TheoBounac/TP-1-Arret-Urgence/images/boitier_emetteur.png

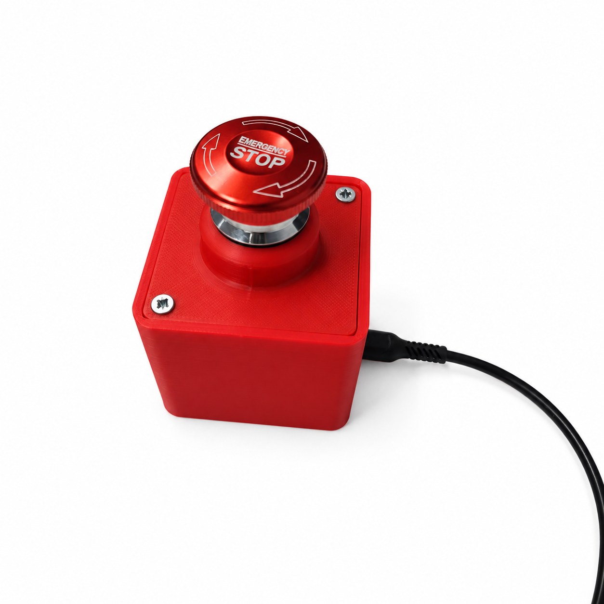
images/boitier_emetteur.png
