TheoBounac/TP-1-Arret-Urgence/images/boitier_recepteur.png

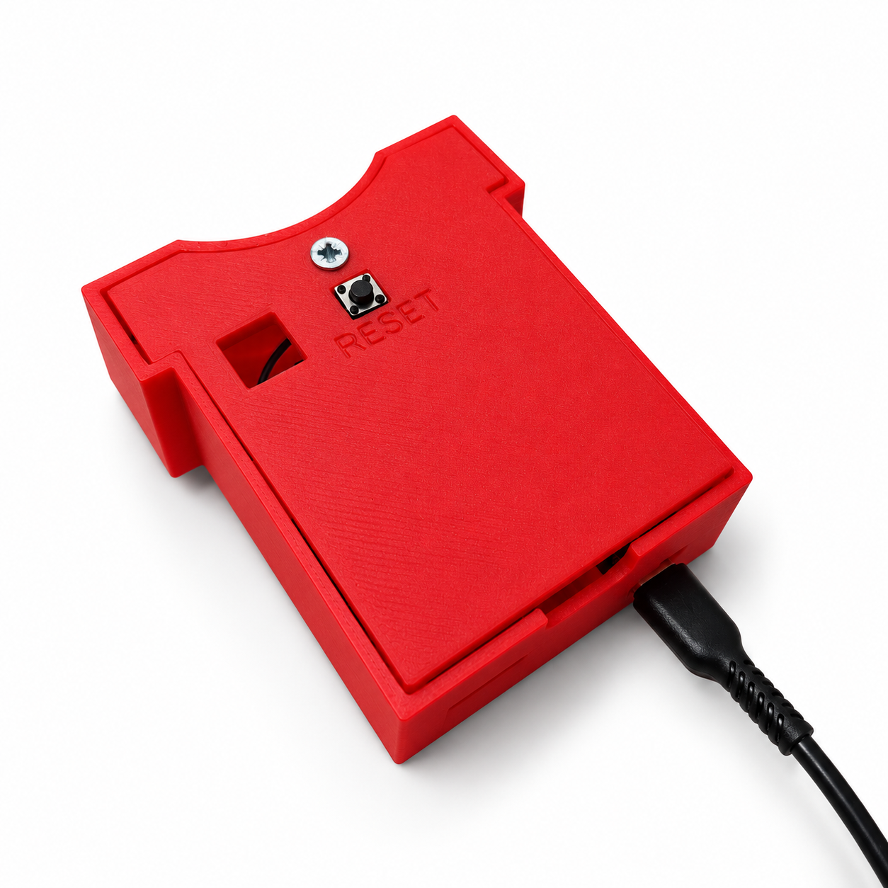
images/boitier_recepteur.png
