TheoBounac/TP-1-Arret-Urgence/images/carte_arduino.png

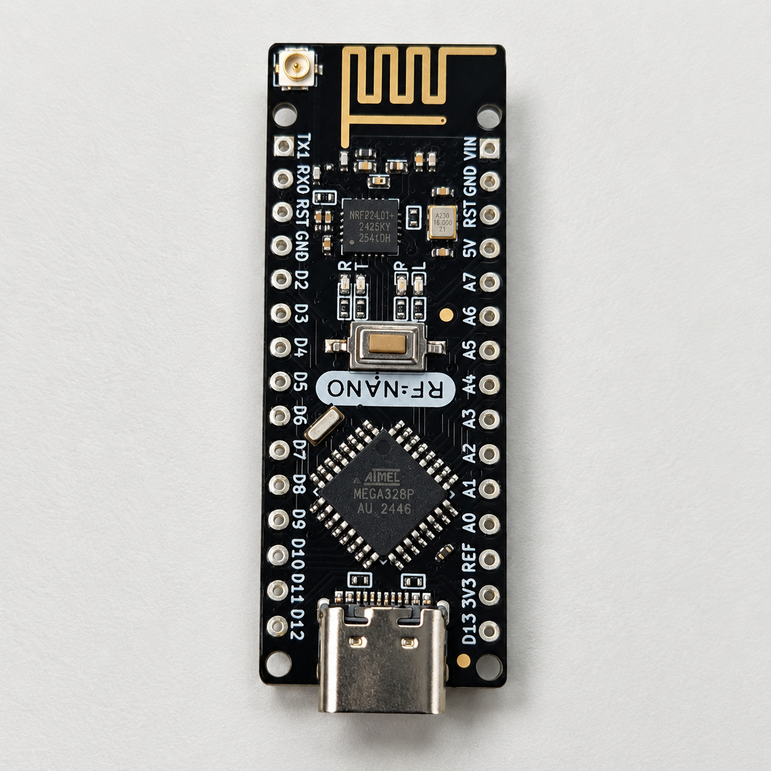
images/carte_arduino.png
