TheoBounac/TP-1-Arret-Urgence/images/cas.png

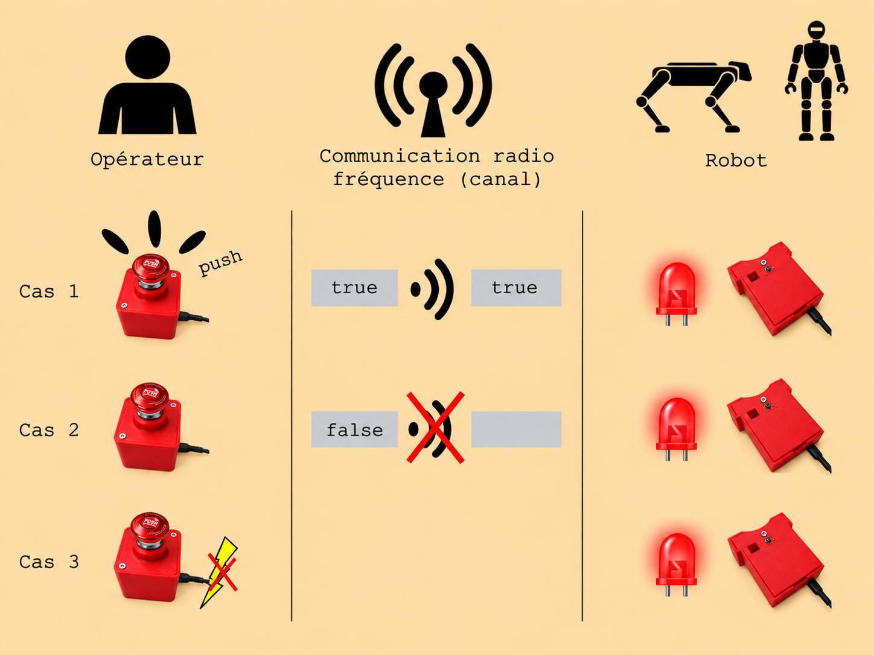
images/cas.png
