TheoBounac/TP-1-Arret-Urgence/images/cas_2.png

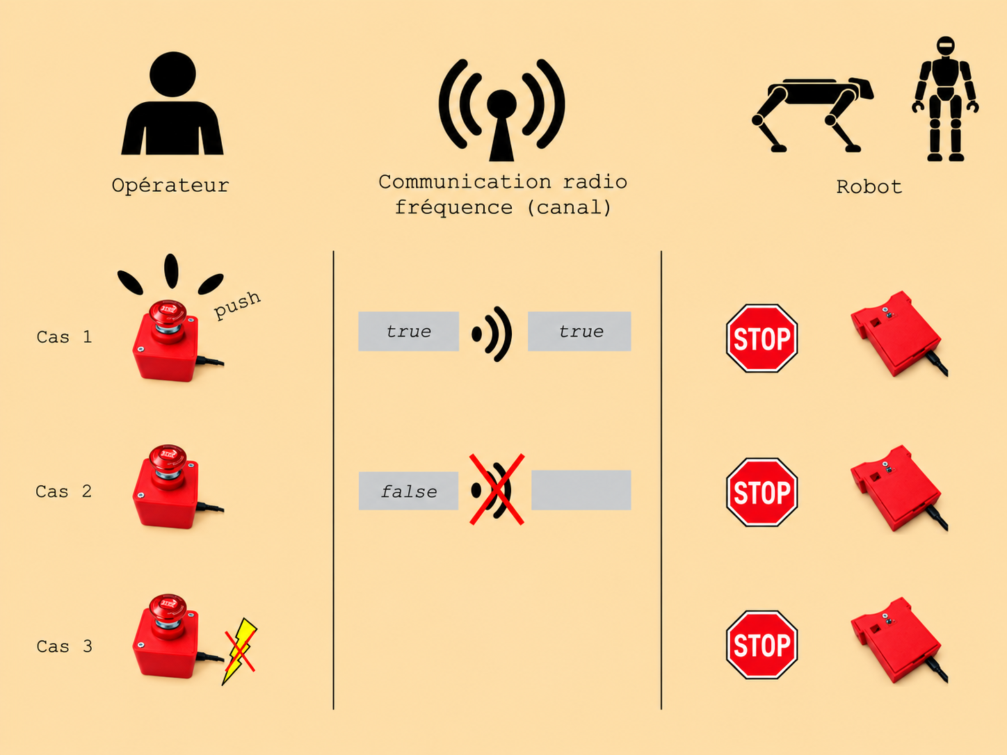
images/cas_2.png
