TheoBounac/TP-1-Arret-Urgence/images/go2.png

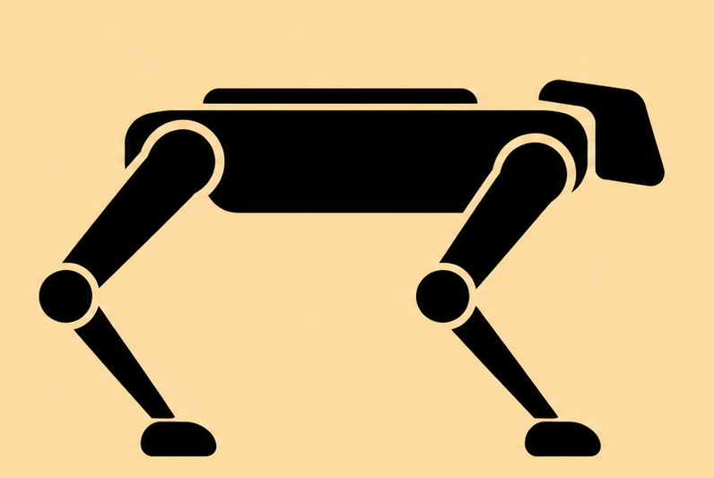
images/go2.png
