TheoBounac/TP-1-Arret-Urgence/images/images.jpeg

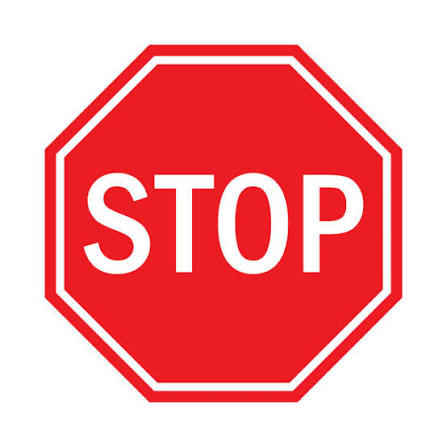
images/images.jpeg
