TheoBounac/TP-1-Arret-Urgence/images/just-got-my-unitree-quadruped-robot-go2-walking-in-isaac-v0-8nw8yerlim7g1.png

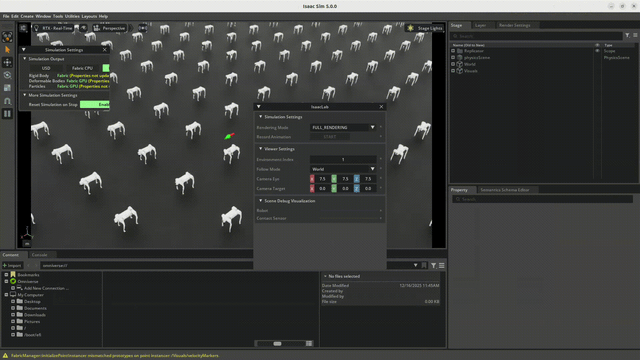
images/just-got-my-unitree-quadruped-robot-go2-walking-in-isaac-v0-8nw8yerlim7g1.png
