TheoBounac/TP-1-Arret-Urgence/images/orig.webp

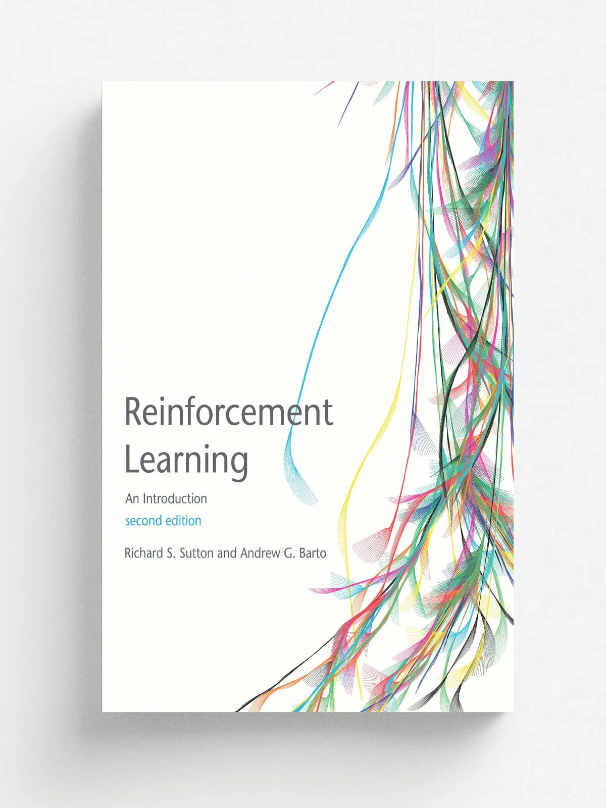
images/orig.webp
