TheoBounac/TP-1-Arret-Urgence/images/receptteur_cable.png

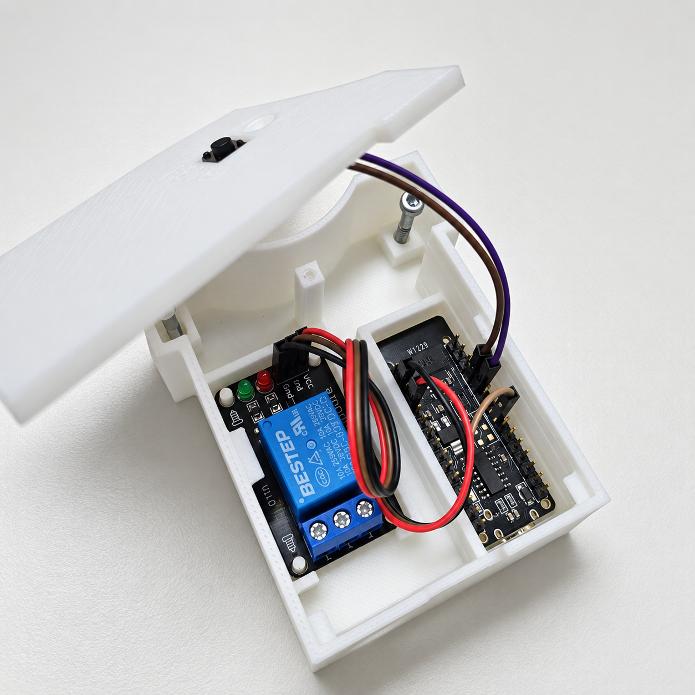
images/receptteur_cable.png
