TheoBounac/TP-1-Arret-Urgence/images/relais_ex.png

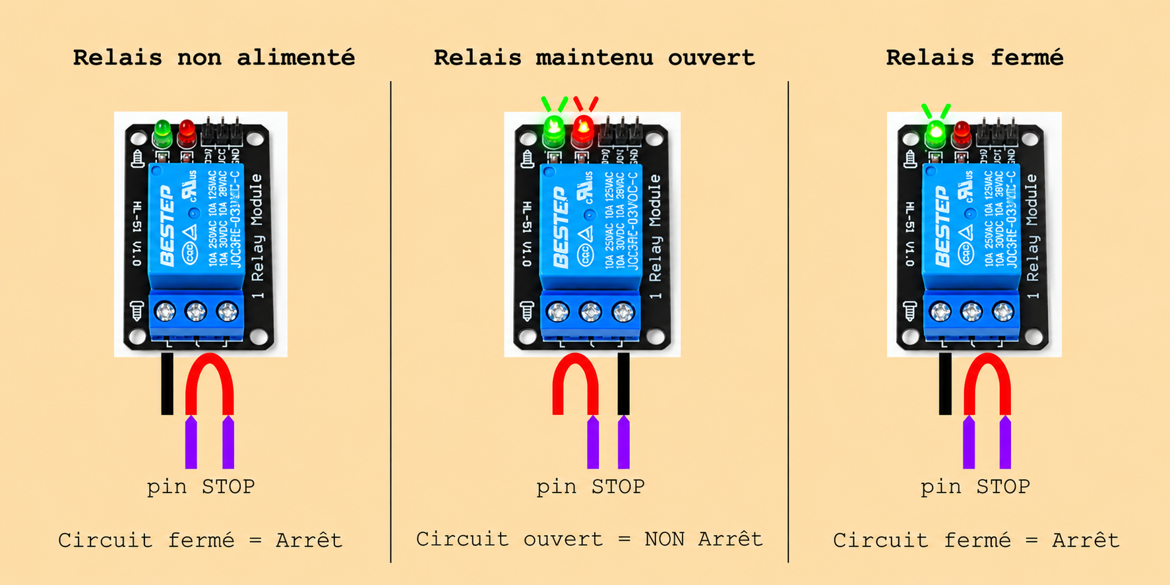
images/relais_ex.png
