TheoBounac/TP-1-Arret-Urgence/images/robots.png

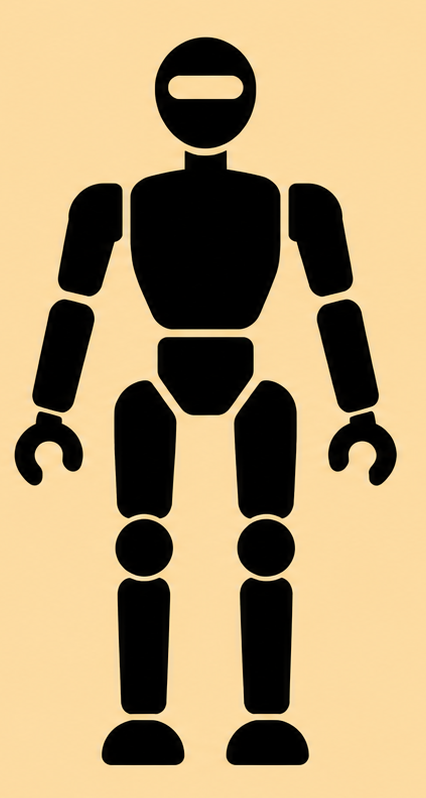
images/robots.png
