TheoBounac/TP-1-Arret-Urgence/images/schema.png

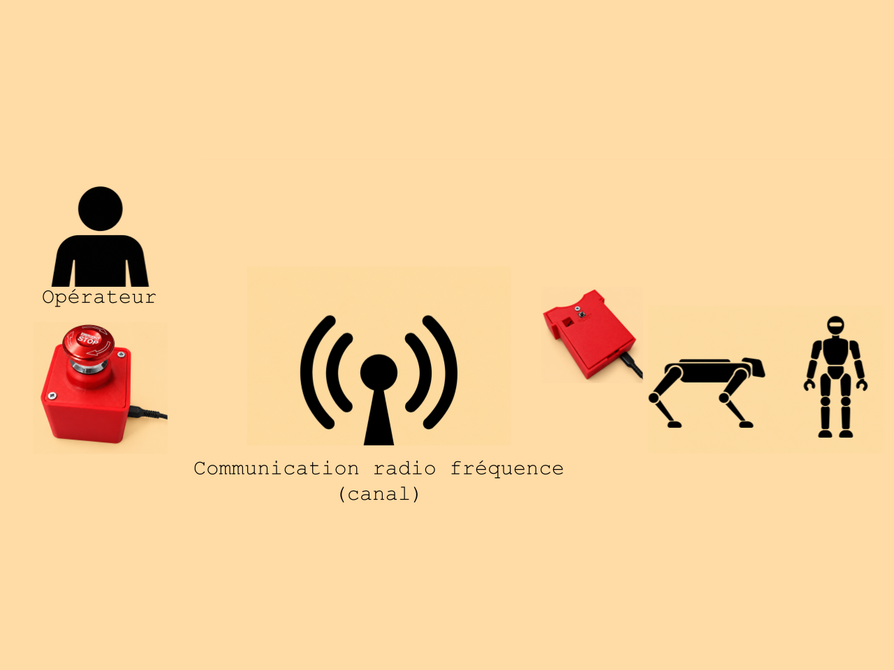
images/schema.png
