TheoBounac/TP-1-Arret-Urgence/images/Tp1 (copy).png

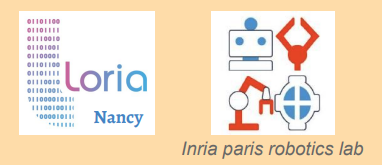
images/Tp1 (copy).png
